OFreddy/wifi-tft-rf24L01/firmware/include/app.h

#pragma once

// Wifi

#include <Ticker.h>

// HTTP Request
#include <AsyncHTTPRequest_Generic.hpp>

// Button
#include <Bounce2.h>

// Sunset
#include "SunsetClass.h"

// TFT
#include "MiniGrafx.h"   // General graphic library
#include "ILI9341_SPI.h" // Hardware-specific library

// JSON
#include <ArduinoJson.h>

#include "user_config.h"

#include "web.h"

class web;

class app
{
public:
    app();
    ~app();

    void setup();
    void loop(bool bDisableUpdate = false);

    uint32_t getUnixTimeStamp();

protected:
private:
    // version
    char mVersion[12];

    // Wifi control
    unsigned long reconnectMillis = 0; // will store last time of WiFi reconnection retry
    unsigned long reconnectProgressMillis = 0;
    int wifiConnectProgress;
    wl_status_t oldWifiStatus = WL_IDLE_STATUS; // Wifi status indication

    // NTP Service, time and sunset
    time_t mTimestamp;
    Ticker *mUptimeTicker;
    uint16_t mUptimeInterval;
    uint32_t mUptimeSecs;

    // Http Service
    AsyncHTTPRequest *mHttpReq;
    Ticker *mHttpReqTicker;

    IPAddress mHttpServerIP;
    uint32_t mHttpReqTick;
    uint16_t mHttpReqInterval;

    // Button
    Bounce2::Button *buttonBounce = NULL;

    // Display on/off
    bool displayOn, displayState;
    uint32_t displayDelay;

    // TFT Display
    ILI9341_SPI *tft;
    MiniGrafx *gfx;

    // General
    void cyclicTick(void);
    void httpReqTick(void);

    // Web sites
    web *mWebInst;

    // Web services
    static void httpRequestCb(void *optParm, AsyncHTTPRequest *request, int readyState);
    void getHttpData(void);
    void processHttpData(AsyncHTTPRequest *request);

    // Support functions
    void controlDisplay(void);
    void formatEng(char *dest, float val);

    // Display
    void drawProgress(uint8_t percentage, String text);
    void drawWifiQuality(void);
    void drawTime(void);
    void updateDisplay(void);
    void commitDisplay(void);
};
