OFreddy/wifi-tft-rf24L01/firmware/src/confignetwork.cpp

/*
 Copyright (C)
    2022            OFreddy

 This program is free software; you can redistribute it and/or
 modify it under the terms of the GNU General Public License
 version 3 as published by the Free Software Foundation.
*/

#include "utils.h"
#include "config.h"
#include "confignetwork.h"

///////////////////////////////////////////////////////////////////////////////////////////////////////////////////////

String ConfigNetworkClass::GetHostname()
{
    const CONFIG_T& config = ConfigInst.get();
    char preparedHostname[WIFI_MAX_HOSTNAME_STRLEN + 1];
    char resultHostname[WIFI_MAX_HOSTNAME_STRLEN + 1];
    uint8_t pos = 0;

    uint32_t chipId = Utils::getChipId();
    snprintf(preparedHostname, WIFI_MAX_HOSTNAME_STRLEN + 1, config.WiFi_Hostname, chipId);

    const char* pC = preparedHostname;
    while (*pC && pos < WIFI_MAX_HOSTNAME_STRLEN) { // while !null and not over length
        if (isalnum(*pC)) { // if the current char is alpha-numeric append it to the hostname
            resultHostname[pos] = *pC;
            pos++;
        } else if (*pC == ' ' || *pC == '_' || *pC == '-' || *pC == '+' || *pC == '!' || *pC == '?' || *pC == '*') {
            resultHostname[pos] = '-';
            pos++;
        }
        // else do nothing - no leading hyphens and do not include hyphens for all other characters.
        pC++;
    }

    resultHostname[pos] = '\0'; // terminate string

    // last character must not be hyphen
    while (pos > 0 && resultHostname[pos - 1] == '-') {
        resultHostname[pos - 1] = '\0';
        pos--;
    }

    // Fallback if no other rule applied
    if (strlen(resultHostname) == 0) {
        snprintf(resultHostname, WIFI_MAX_HOSTNAME_STRLEN + 1, APP_HOSTNAME, chipId);
    }

    return resultHostname;
}


///////////////////////////////////////////////////////////////////////////////////////////////////////////////////////

ConfigNetworkClass ConfigNetworkInst; // Network class instance singleton

///////////////////////////////////////////////////////////////////////////////////////////////////////////////////////
/// End of file
///////////////////////////////////////////////////////////////////////////////////////////////////////////////////////
